minou65/NMEA2000-Relaybox/src/favicon.h

// favicon.h

#ifndef _FAVICON_h
#define _FAVICON_h

#if defined(ARDUINO) && ARDUINO >= 100
#include "arduino.h"
#else
#include "WProgram.h"
#endif

const uint8_t favicon_ico[] PROGMEM = { //nmea2000-relay_96x96.png
0x89, 0x50, 0x4E, 0x47, 0x0D, 0x0A, 0x1A, 0x0A, 0x00, 0x00, 0x00, 0x0D, 0x49, 0x48, 0x44, 0x52,
0x00, 0x00, 0x00, 0x60, 0x00, 0x00, 0x00, 0x60, 0x08, 0x06, 0x00, 0x00, 0x00, 0xE2, 0x98, 0x77,
0x38, 0x00, 0x00, 0x00, 0x09, 0x70, 0x48, 0x59, 0x73, 0x00, 0x00, 0x0B, 0x13, 0x00, 0x00, 0x0B,
0x13, 0x01, 0x00, 0x9A, 0x9C, 0x18, 0x00, 0x00, 0x08, 0x26, 0x49, 0x44, 0x41, 0x54, 0x78, 0xDA,
0xED, 0x9D, 0x7B, 0x8C, 0x1F, 0x55, 0x15, 0xC7, 0x3F, 0x67, 0x59, 0x96, 0x6D, 0x31, 0x6B, 0x5D,
0x4B, 0x89, 0x96, 0x52, 0x23, 0xD2, 0x94, 0x5A, 0xF0, 0xD1, 0x40, 0xAD, 0xA9, 0xF1, 0x0F, 0x83,
0x0A, 0xA2, 0x10, 0x8D, 0x04, 0xE4, 0xA1, 0x42, 0x41, 0x1E, 0xA6, 0x50, 0x35, 0x6A, 0x45, 0x0D,
0x06, 0x5C, 0x89, 0x26, 0xF5, 0x15, 0x40, 0x0C, 0x2E, 0x0F, 0x1F, 0xD8, 0x46, 0x02, 0xA4, 0x96,
0x2C, 0x98, 0xA6, 0x95, 0x14, 0xCB, 0xA3, 0x3C, 0x94, 0x4D, 0xD3, 0x52, 0xE3, 0xD2, 0xCA, 0xA3,
0xD5, 0xBE, 0xC4, 0x2D, 0xD0, 0xEE, 0xE3, 0xF8, 0xC7, 0x9C, 0x49, 0x6F, 0x27, 0x33, 0xF3, 0x9B,
0xF9, 0xB9, 0xBF, 0xDF, 0xF6, 0x37, 0x7B, 0x4E, 0x72, 0x33, 0x33, 0x77, 0xBE, 0xF7, 0xCE, 0xFC,
0xCE, 0x77, 0xE6, 0x9E, 0x7B, 0xCE, 0xBD, 0x73, 0x7F, 0xA2, 0xAA, 0xB8, 0x8C, 0x9F, 0xB4, 0xB9,
0x0A, 0x9C, 0x00, 0x27, 0xC0, 0xC5, 0x09, 0x98, 0xB0, 0xD2, 0x5E, 0x04, 0x24, 0x22, 0xD7, 0x03,
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
0x16, 0xB8, 0x1E, 0x78, 0x73, 0x90, 0x77, 0xB3, 0xF7, 0x82, 0x9A, 0x24, 0xAA, 0xFA, 0x3D, 0x60,
0x45, 0x90, 0x75, 0x99, 0xAA, 0x3E, 0xE2, 0x04, 0x34, 0x57, 0xEE, 0x0A, 0x08, 0xB9, 0xBD, 0xCA,
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
};
#endif
